mlab-modules/STM32TQ6401/doc/gen/dxf/STM32TQ6401-B_Fab.dxf

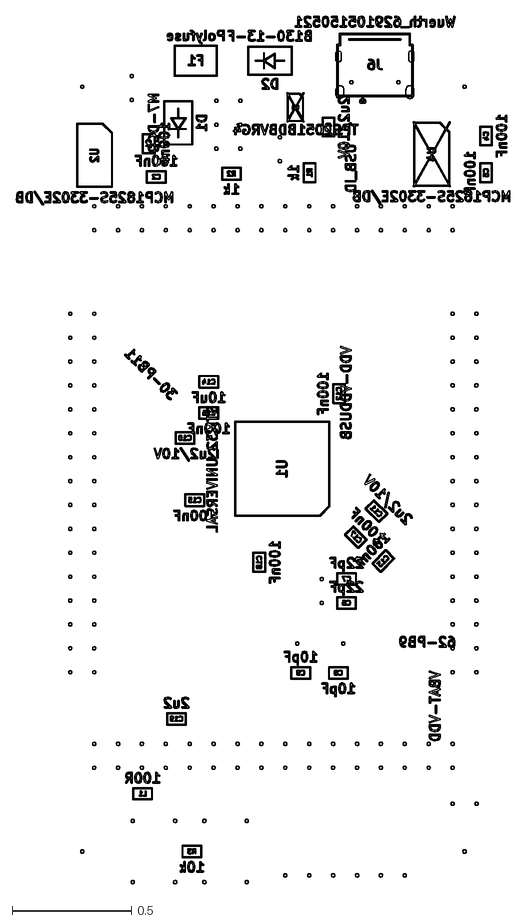
[picture p14: CAD file, 2025-05-06]
doc/gen/dxf/STM32TQ6401-B_Fab.dxf
2.07 x 3.63
