mlab-modules/STM32TQ6401/doc/gen/dxf/STM32TQ6401-F_Cu.dxf

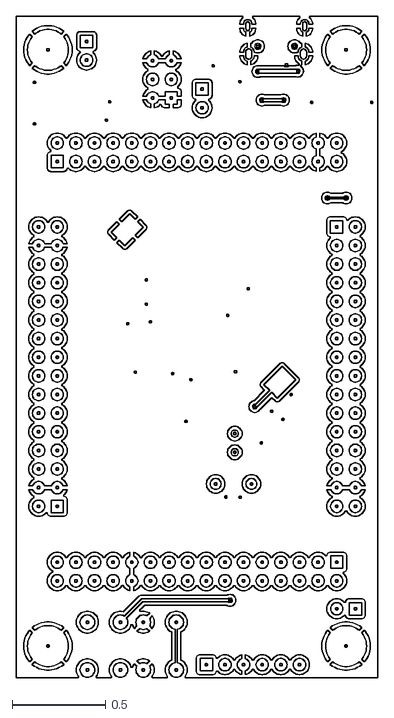
[picture p15: CAD file, 2025-05-06]
doc/gen/dxf/STM32TQ6401-F_Cu.dxf
1.94 x 3.55
