mlab-modules/STM32TQ6401/doc/gen/dxf/STM32TQ6401-F_Courtyard.dxf

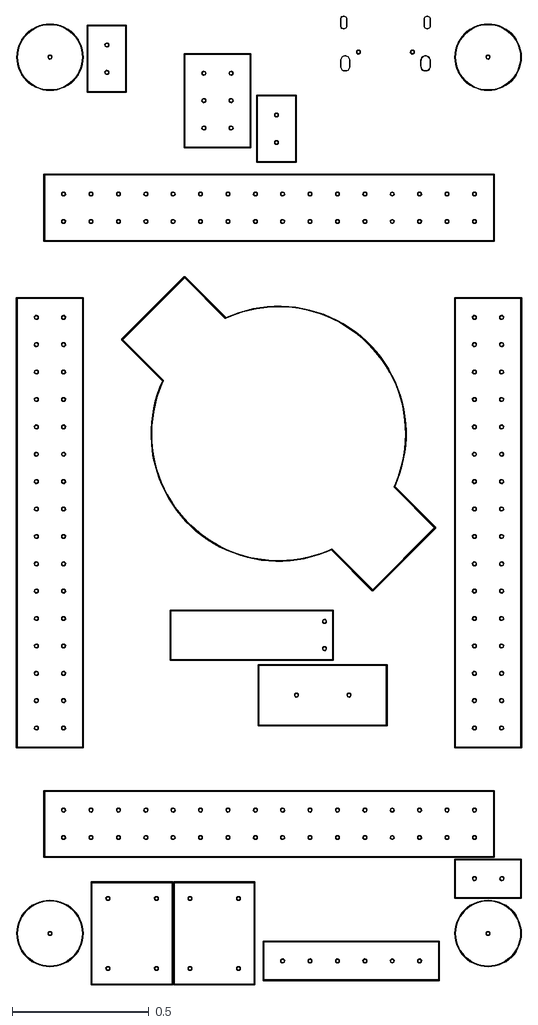
[picture p16: CAD file, 2025-05-06]
doc/gen/dxf/STM32TQ6401-F_Courtyard.dxf
1.84 x 3.54
