mlab-modules/STM32TQ6401/doc/gen/dxf/STM32TQ6401-B_Cu.dxf

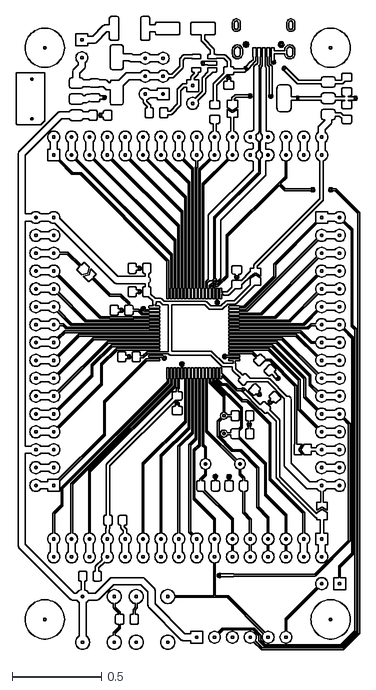
[picture p17: CAD file, 2025-05-06]
doc/gen/dxf/STM32TQ6401-B_Cu.dxf
1.92 x 3.54
